Nauman3S/SmartOEESystem/artwork/cdb1.png

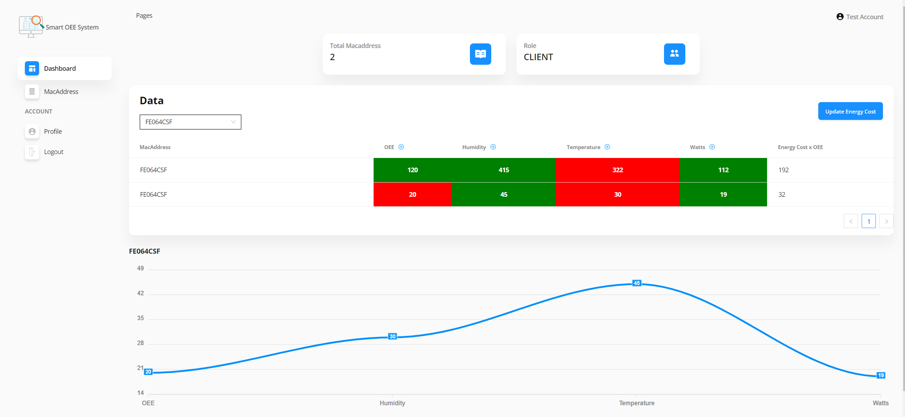
artwork/cdb1.png
