Nauman3S/SmartOEESystem/artwork/cdb2.png

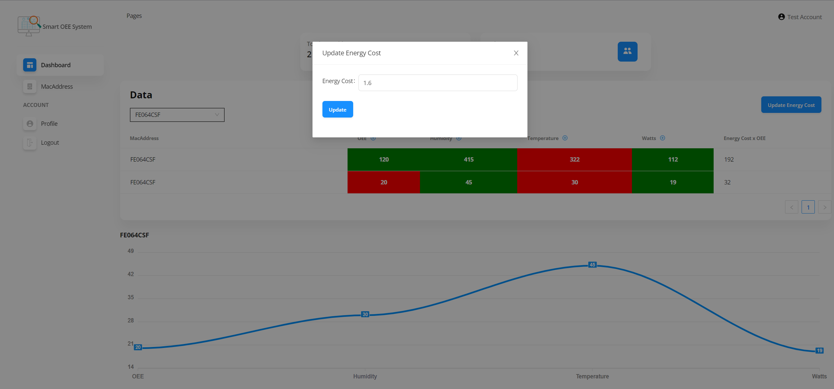
artwork/cdb2.png
