Nauman3S/SmartOEESystem/artwork/cdb3.png

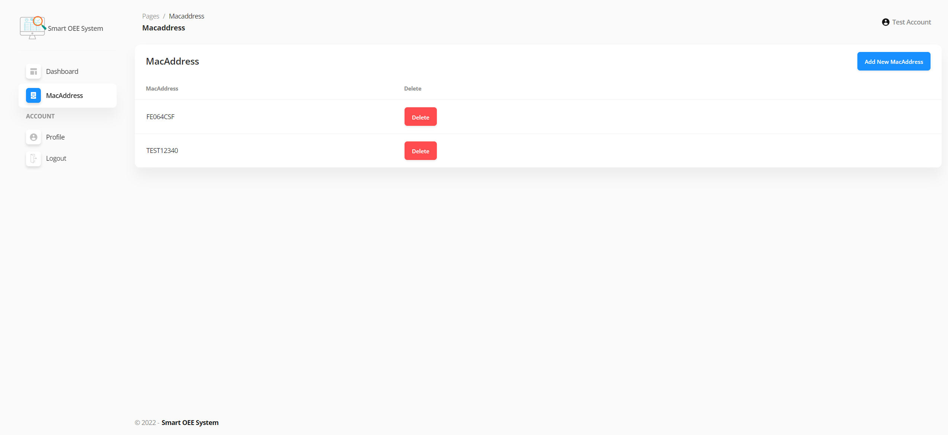
artwork/cdb3.png
