Nauman3S/SmartOEESystem/artwork/cdb4.png

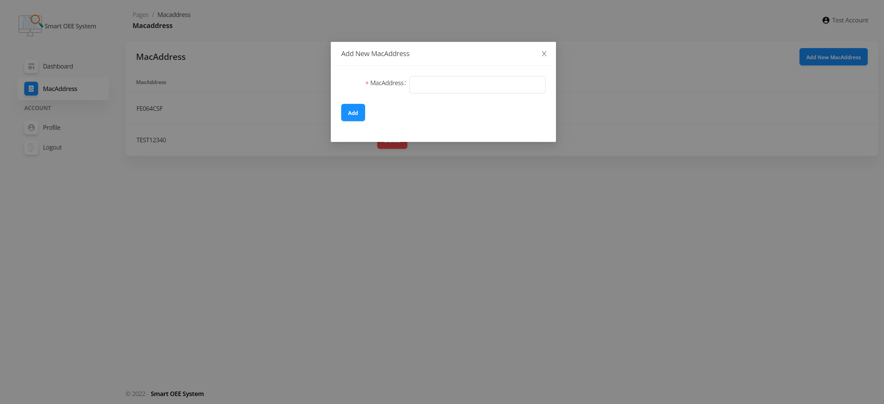
artwork/cdb4.png
