Nauman3S/SmartOEESystem/artwork/db1.png

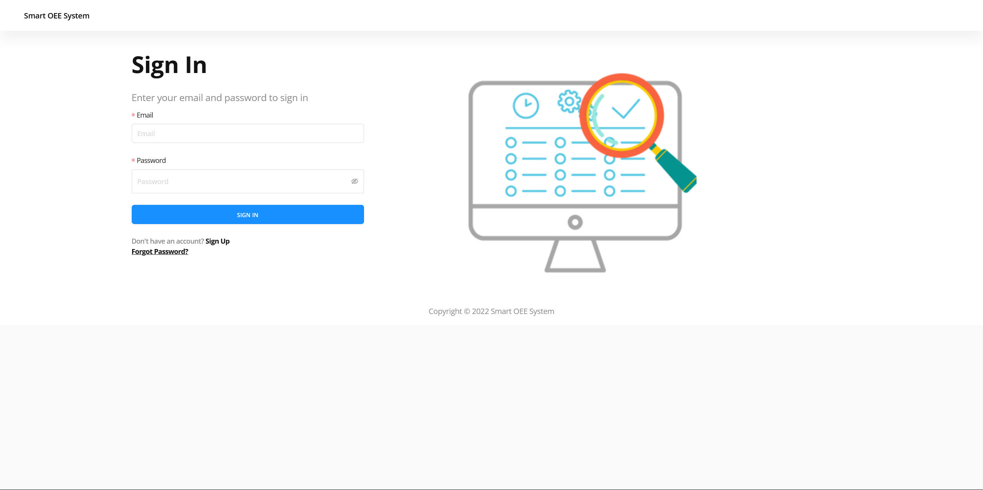
artwork/db1.png
