Nauman3S/SmartOEESystem/artwork/db2.png

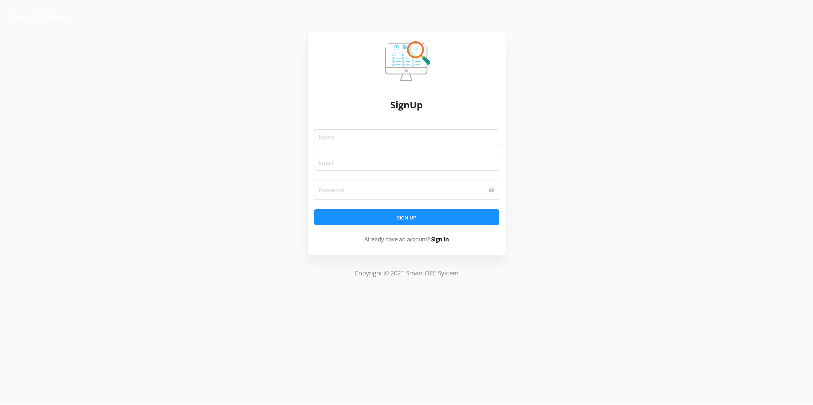
artwork/db2.png
