Nauman3S/SmartOEESystem/artwork/db3.png

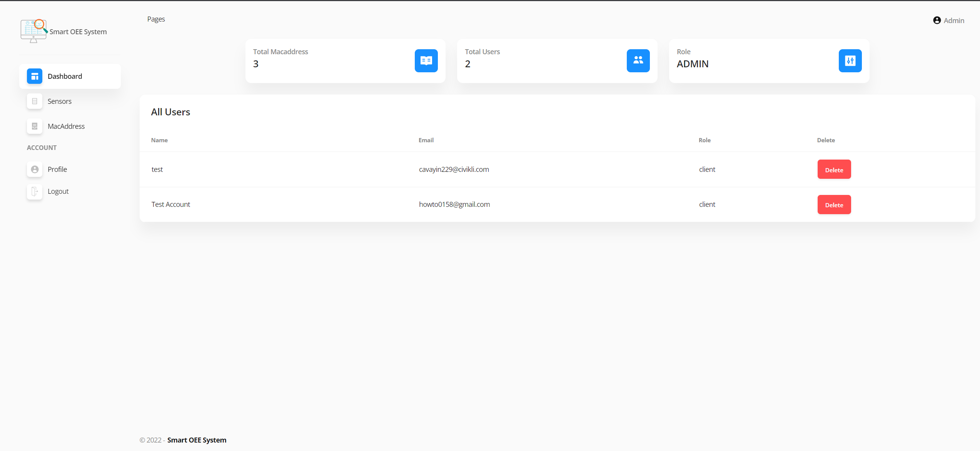
artwork/db3.png
