Nauman3S/SmartOEESystem/artwork/db4.png

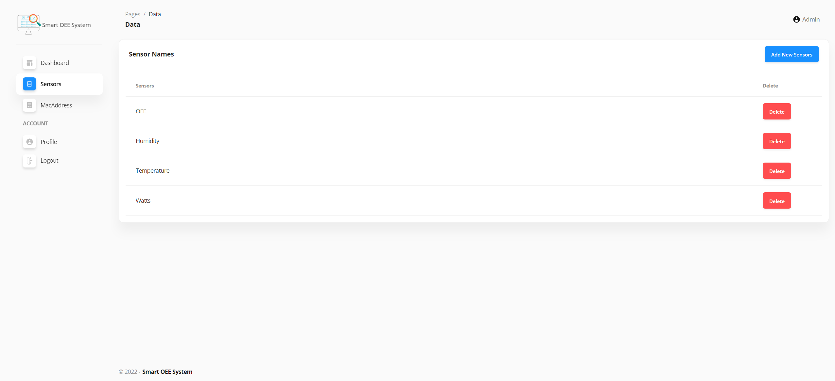
artwork/db4.png
