Nauman3S/SmartOEESystem/artwork/db5.png

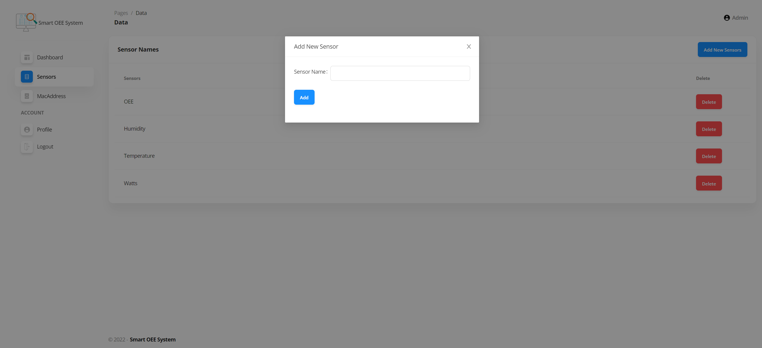
artwork/db5.png
