Nauman3S/SmartOEESystem/artwork/db6.png

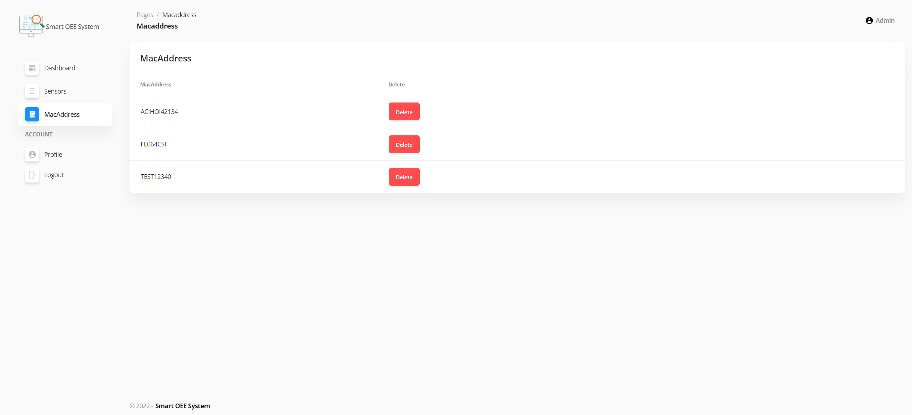
artwork/db6.png
