Nauman3S/SmartOEESystem/artwork/scr2.jpg

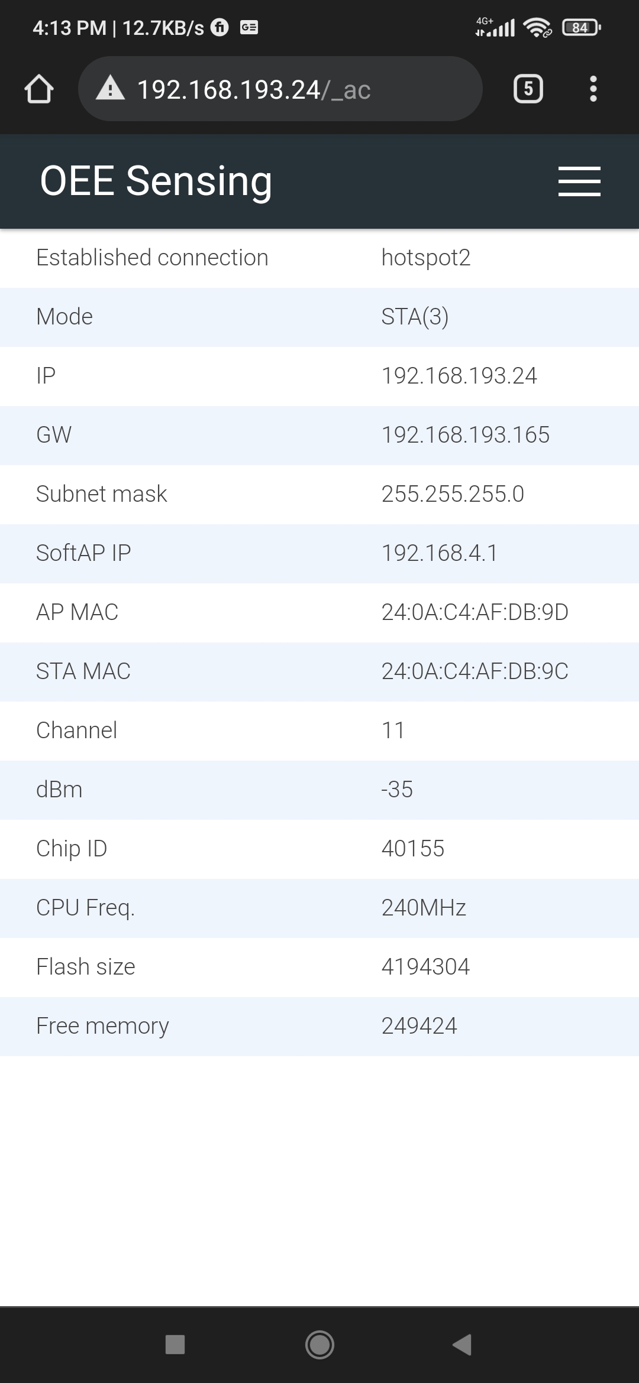
artwork/scr2.jpg
