Nauman3S/SmartOEESystem/artwork/scr3.png

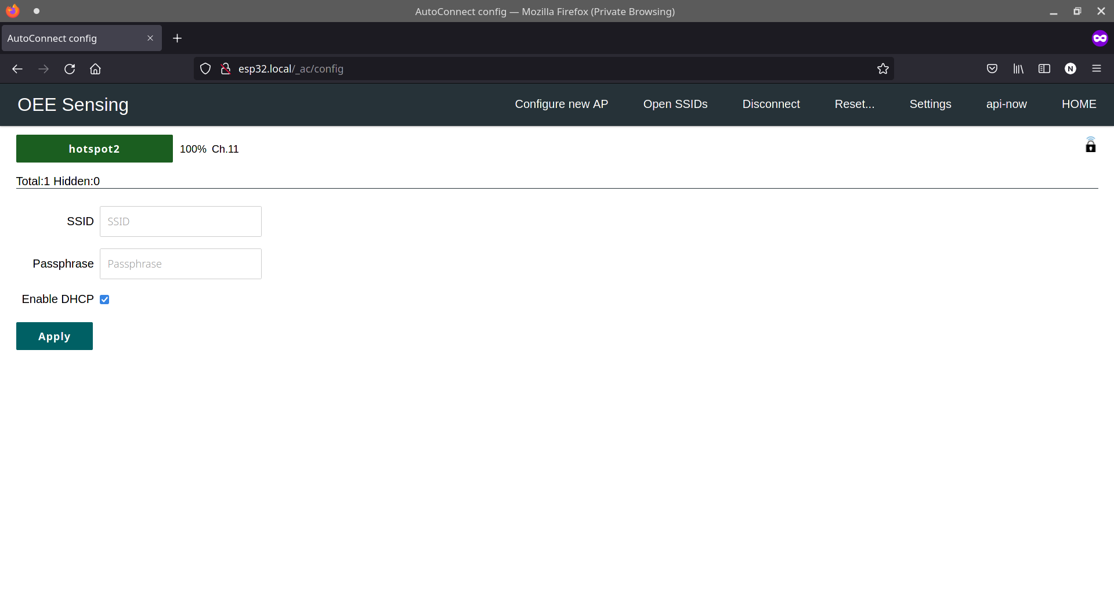
artwork/scr3.png
