Nauman3S/SmartOEESystem/artwork/scr5.png

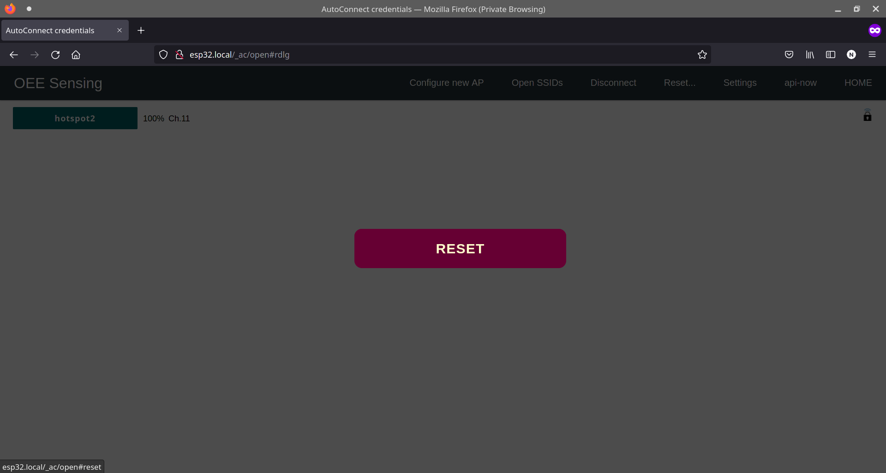
artwork/scr5.png
