Nauman3S/SmartOEESystem/artwork/scr6.png

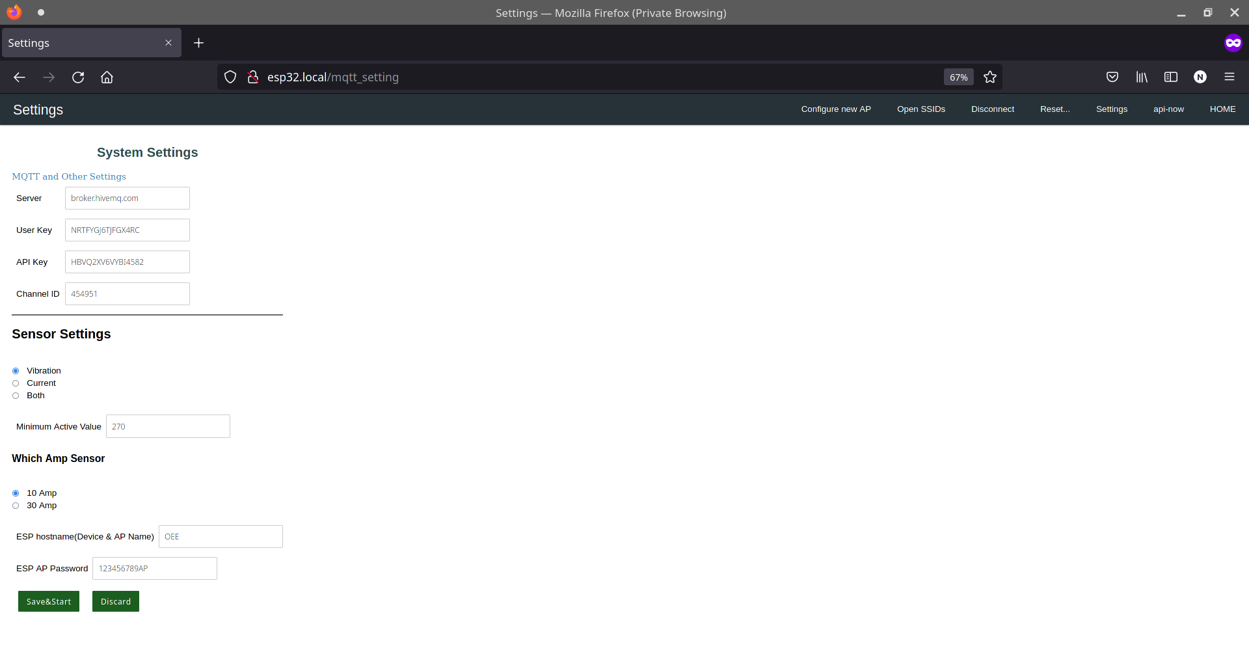
artwork/scr6.png
