Nauman3S/SmartOEESystem/artwork/scr7.png

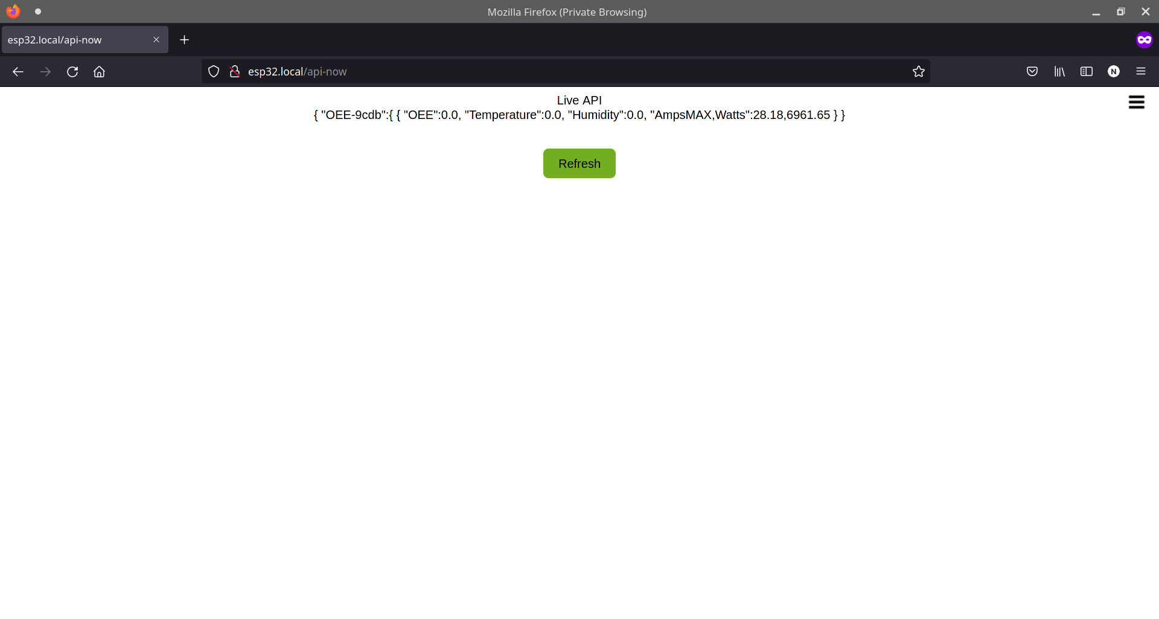
artwork/scr7.png
