Nauman3S/SmartOEESystem/artwork/scr8.png

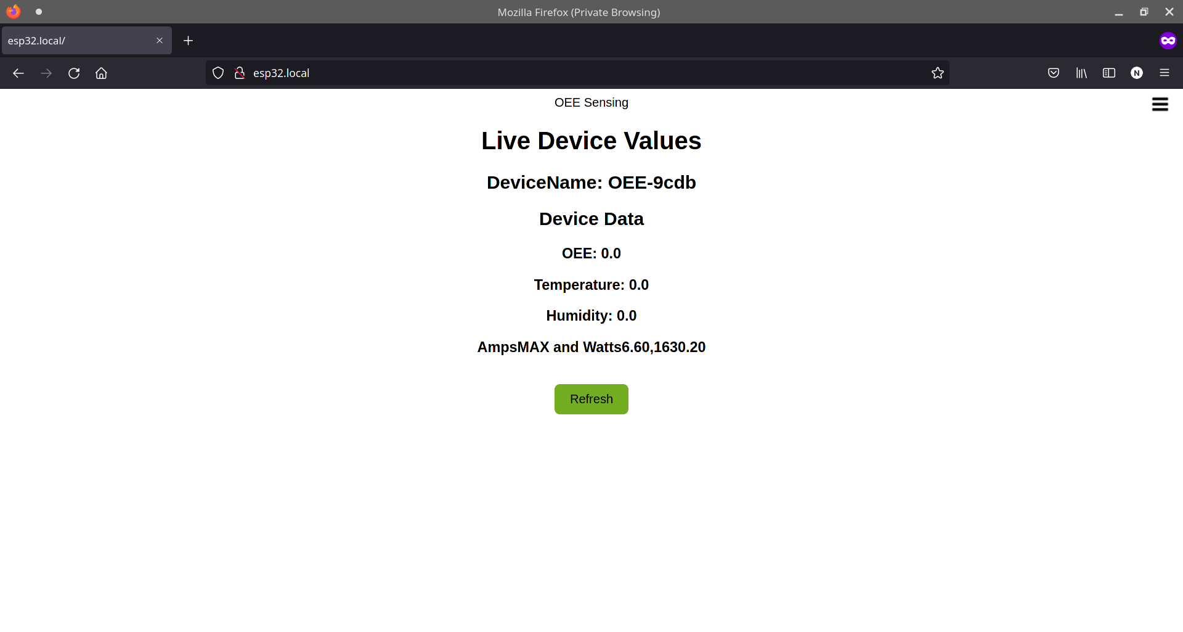
artwork/scr8.png
