Nauman3S/SmartOEESystem/artwork/scr9.png

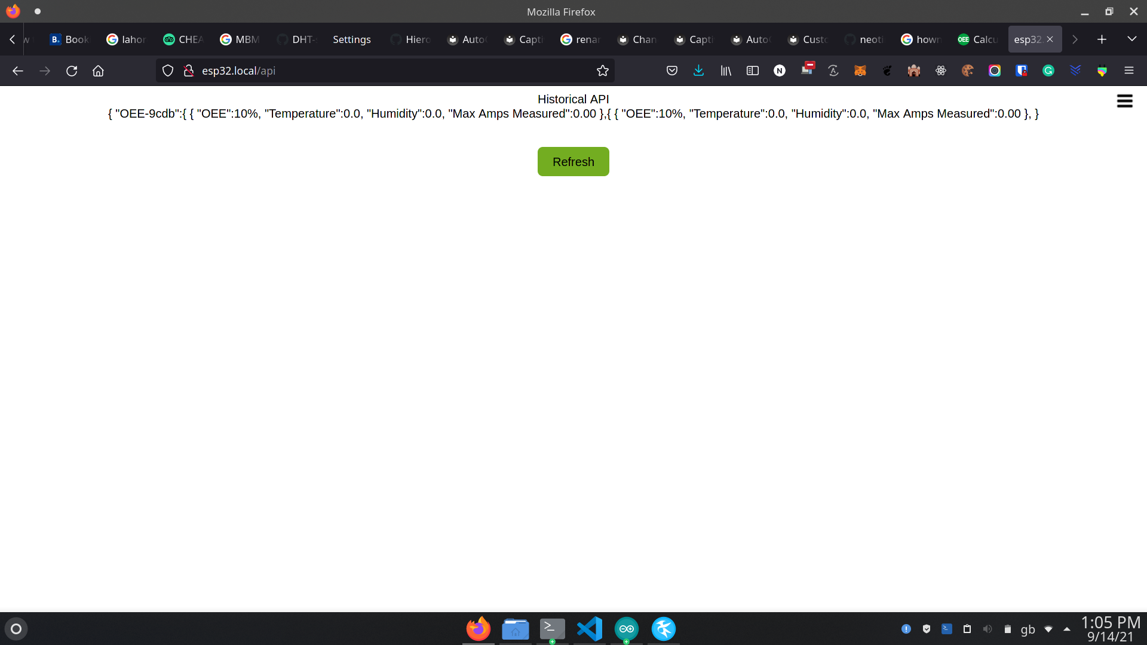
artwork/scr9.png
