Nauman3S/SmartOEESystem/artwork/scr10.png

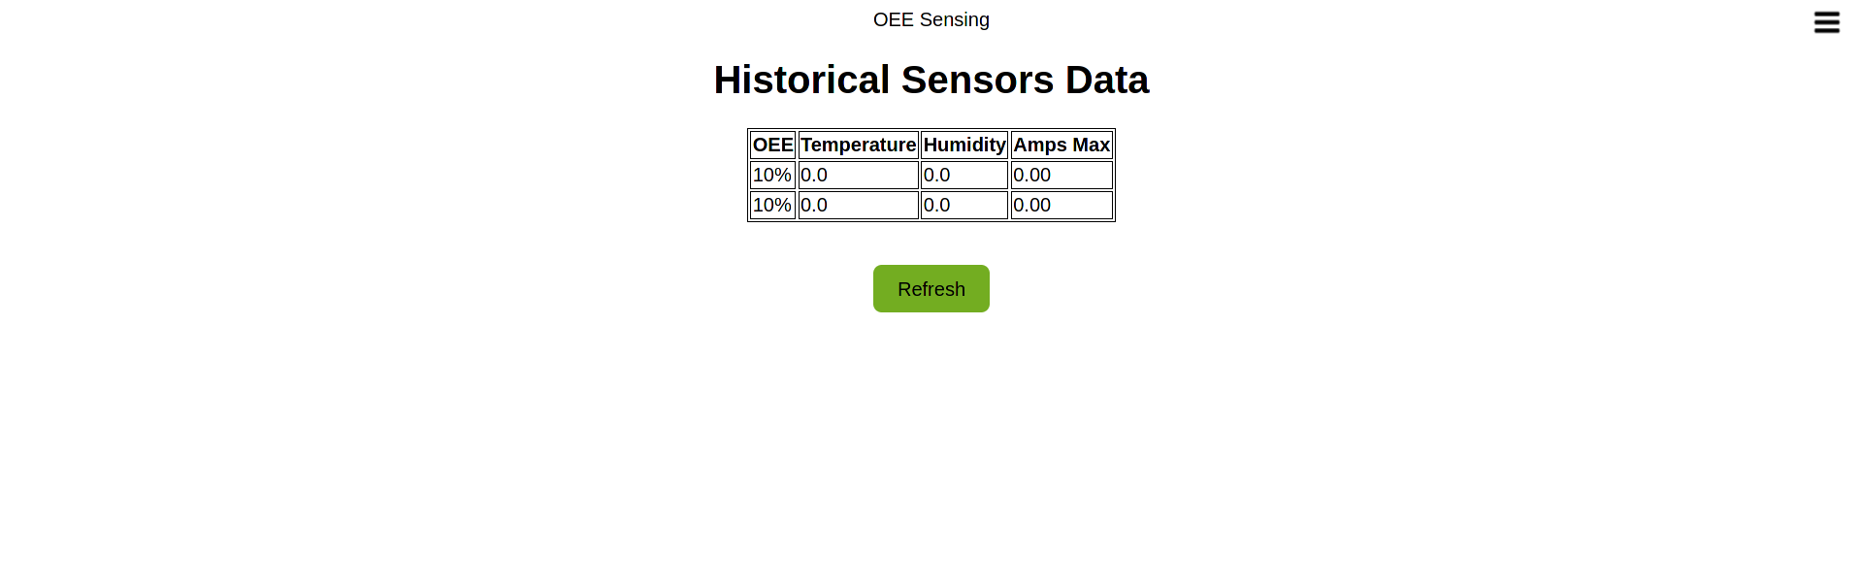
artwork/scr10.png
