Nauman3S/SmartOEESystem/Circuit/ds18b20.jpg

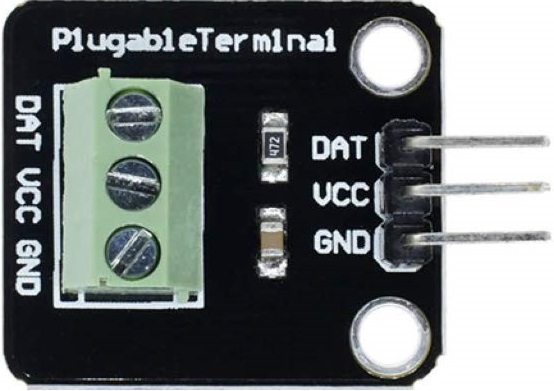
Circuit/ds18b20.jpg
