Nauman3S/SmartOEESystem/Circuit/PCB/pcb_b.png

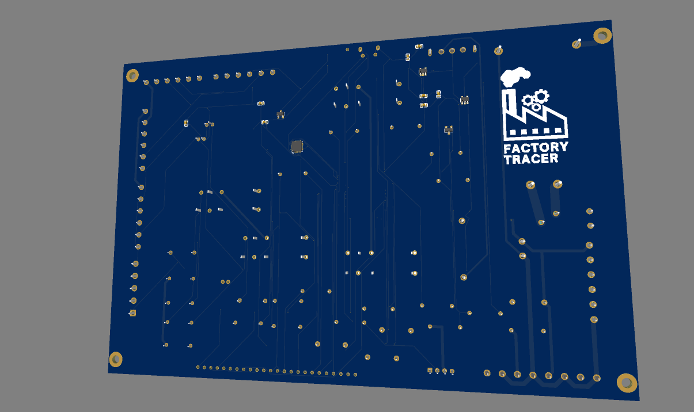
Circuit/PCB/pcb_b.png
