Nauman3S/SmartOEESystem/Circuit/PCB/pcb_f.png

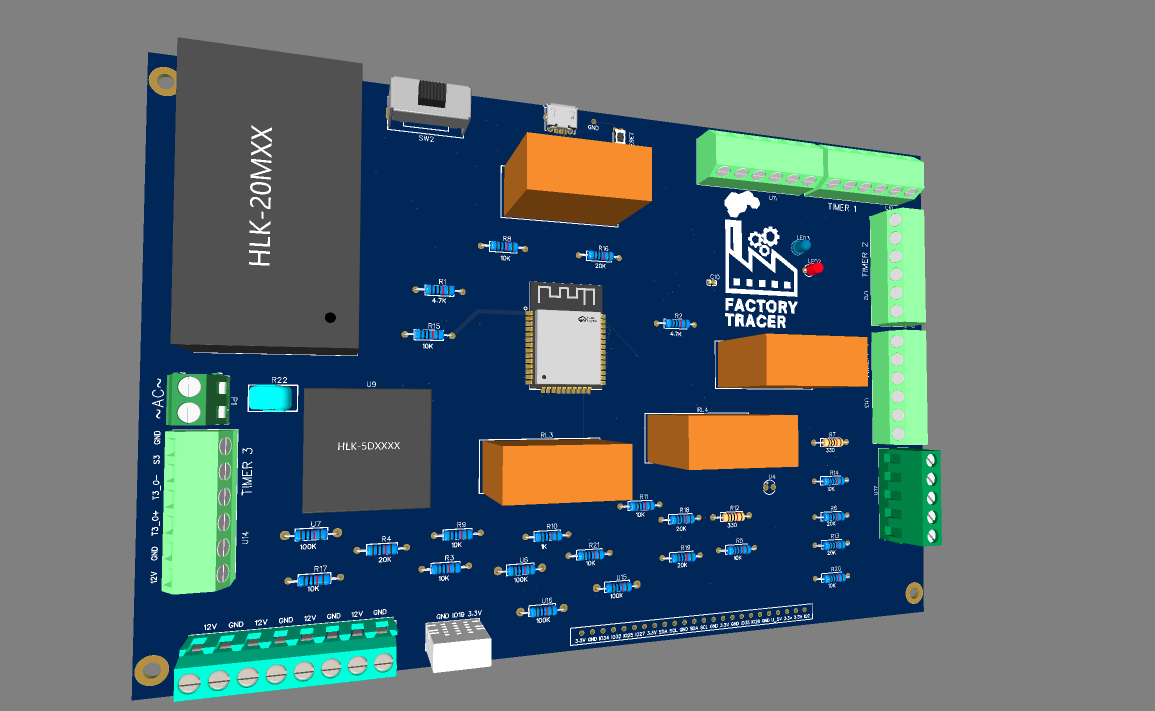
Circuit/PCB/pcb_f.png
