Nauman3S/SmartOEESystem/Circuit/pes.jpg

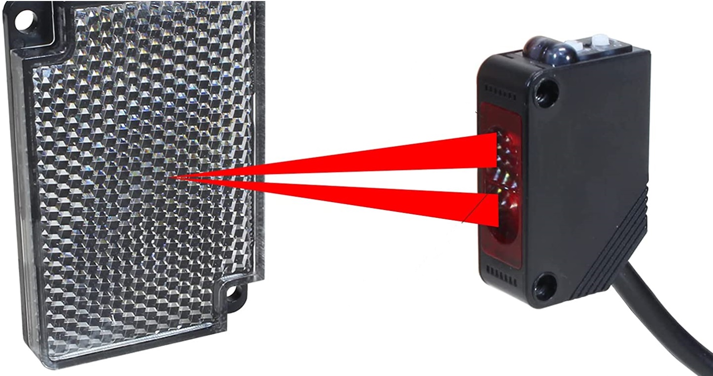
Circuit/pes.jpg
