Nauman3S/SmartOEESystem/temp/Diagram (4).jpg

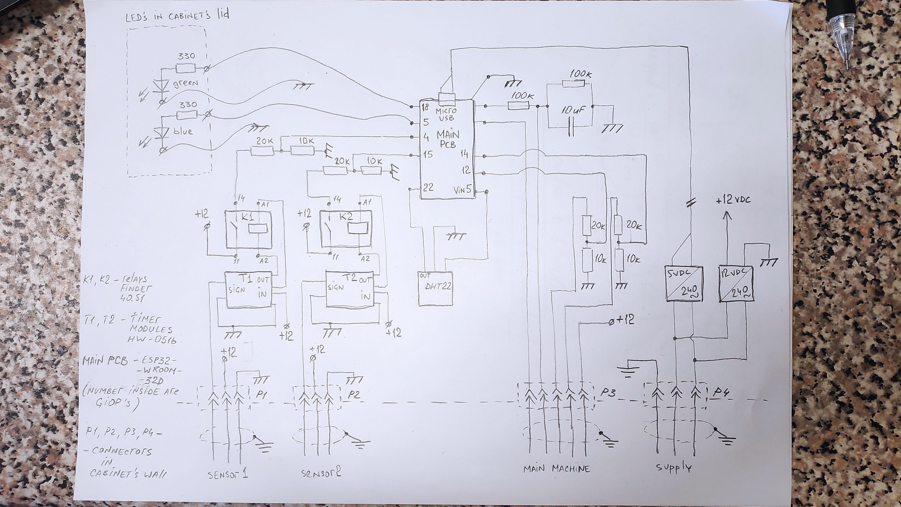
temp/Diagram (4).jpg
