Nauman3S/SmartOEESystem/temp/IOT 2.png

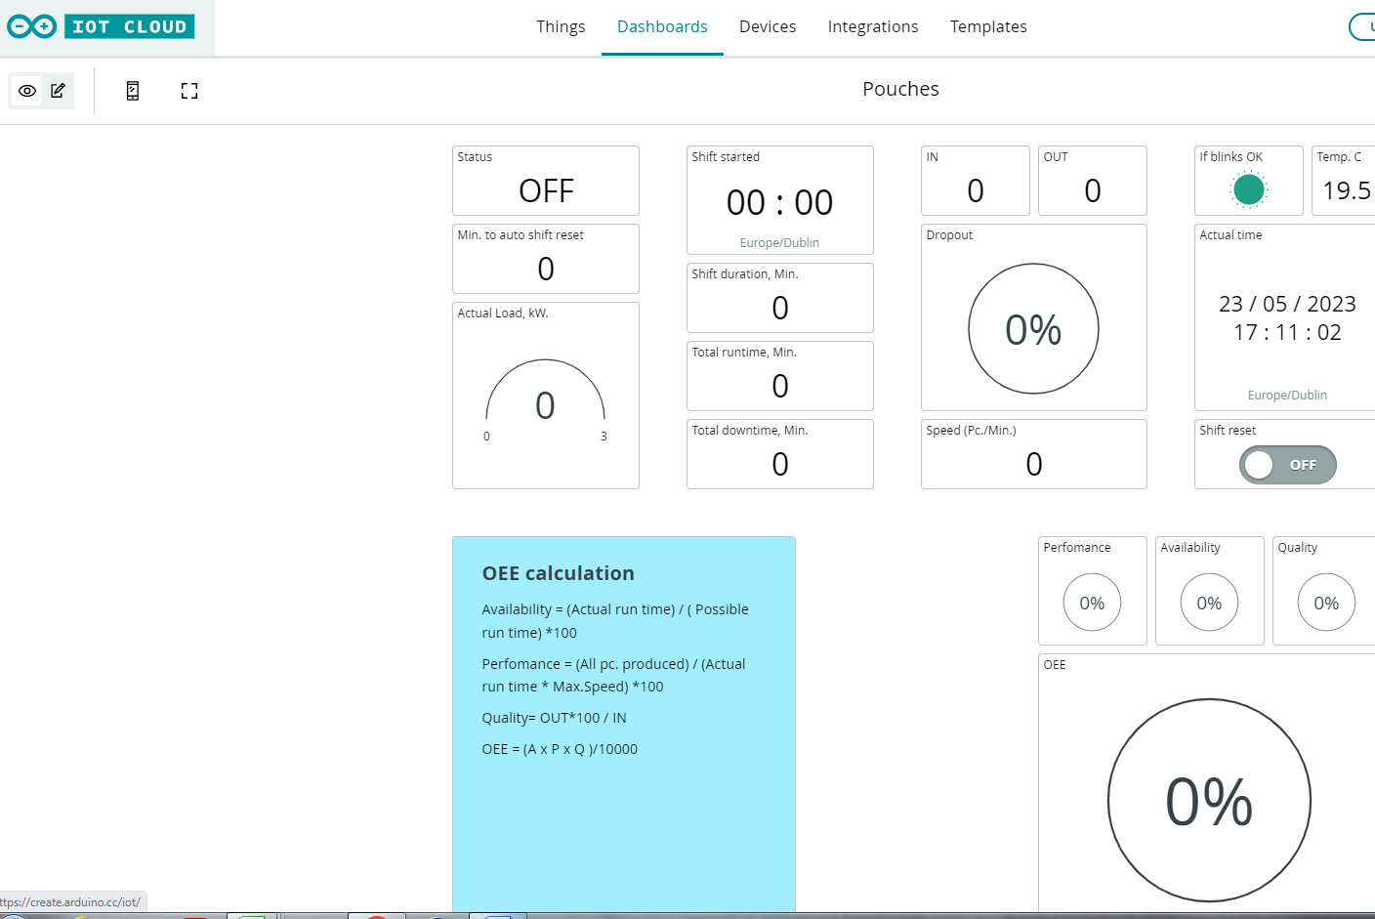
temp/IOT 2.png
