Nauman3S/SmartOEESystem/temp/IOT 3.png

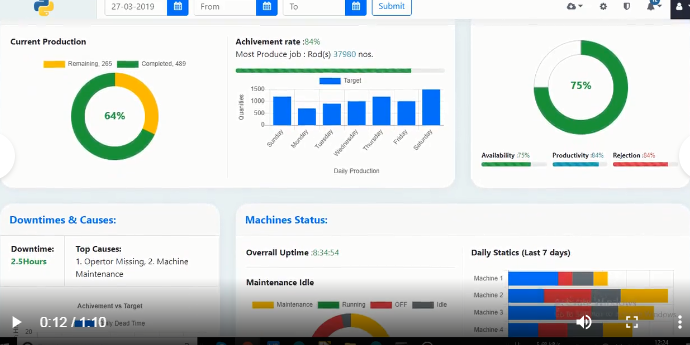
temp/IOT 3.png
