Nauman3S/SmartOEESystem/temp/Line 1.jpg

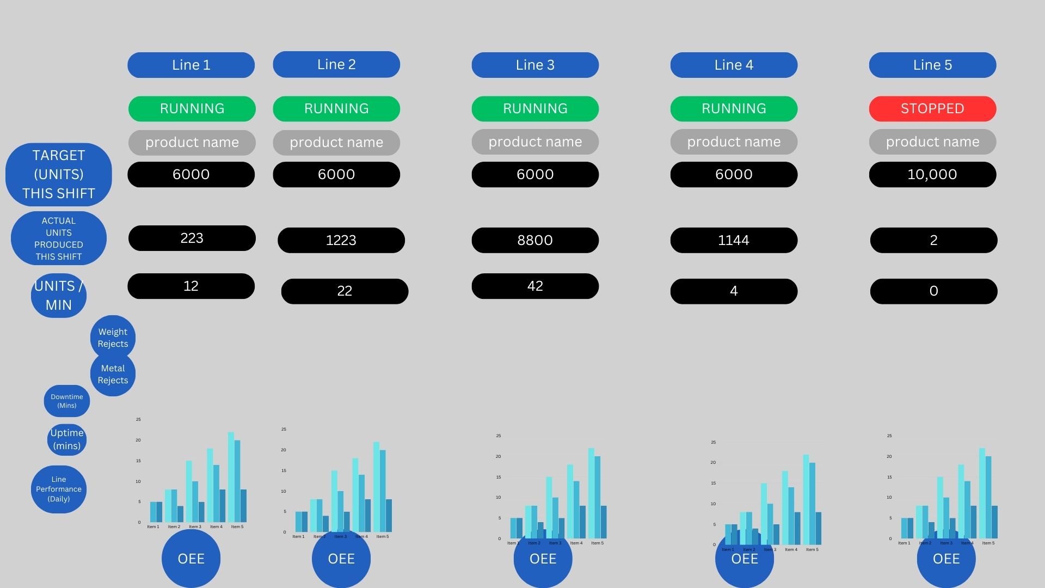
temp/Line 1.jpg
