Nauman3S/SmartOEESystem/temp/paper-dashboard-pro-react-v1.3.2 (1)/paper-dashboard-pro-react-v1.3.2/github-assets/html.png

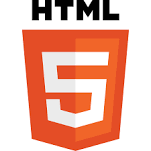
temp/paper-dashboard-pro-react-v1.3.2 (1)/paper-dashboard-pro-react-v1.3.2/github-assets/html.png
