Nauman3S/SmartOEESystem/temp/view (4).jpg

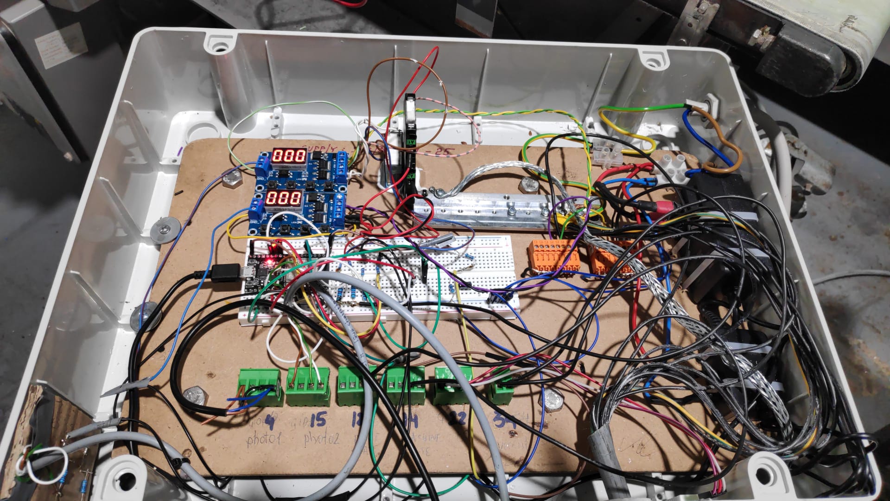
temp/view (4).jpg
