Nauman3S/SmartOEESystem/WebApp/Frontend/src/assets/images/bg-signup.jpg

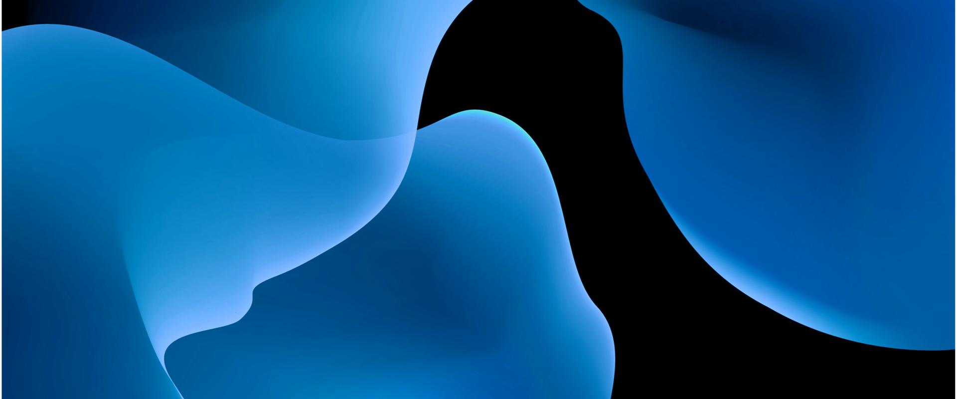
WebApp/Frontend/src/assets/images/bg-signup.jpg
