Nauman3S/SmartOEESystem/WebApp/Frontend/src/assets/images/face-1.jpg

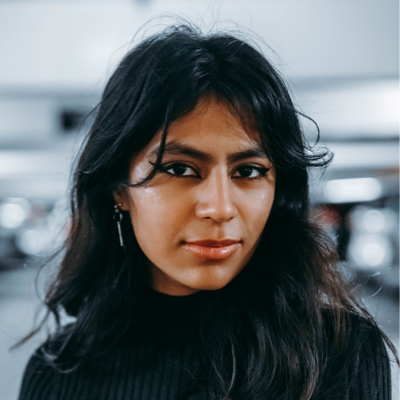
WebApp/Frontend/src/assets/images/face-1.jpg
