Nauman3S/SmartOEESystem/WebApp/Frontend/src/assets/images/face-2.jpg

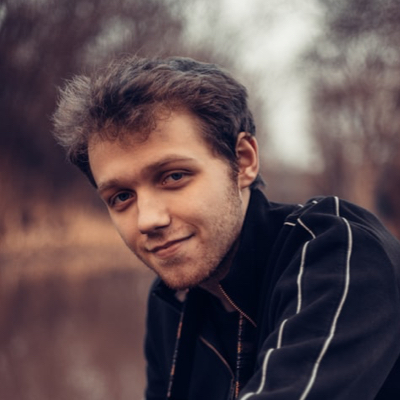
WebApp/Frontend/src/assets/images/face-2.jpg
