Nauman3S/SmartOEESystem/WebApp/Frontend/src/assets/images/face-3.jpg

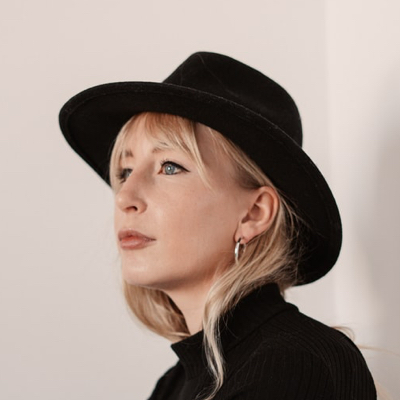
WebApp/Frontend/src/assets/images/face-3.jpg
