Nauman3S/SmartOEESystem/WebApp/Frontend/src/assets/images/face-4.jpg

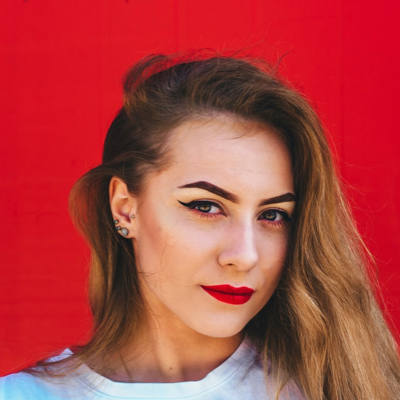
WebApp/Frontend/src/assets/images/face-4.jpg
