Nauman3S/SmartOEESystem/WebApp/Frontend/src/assets/images/face-5.jpeg

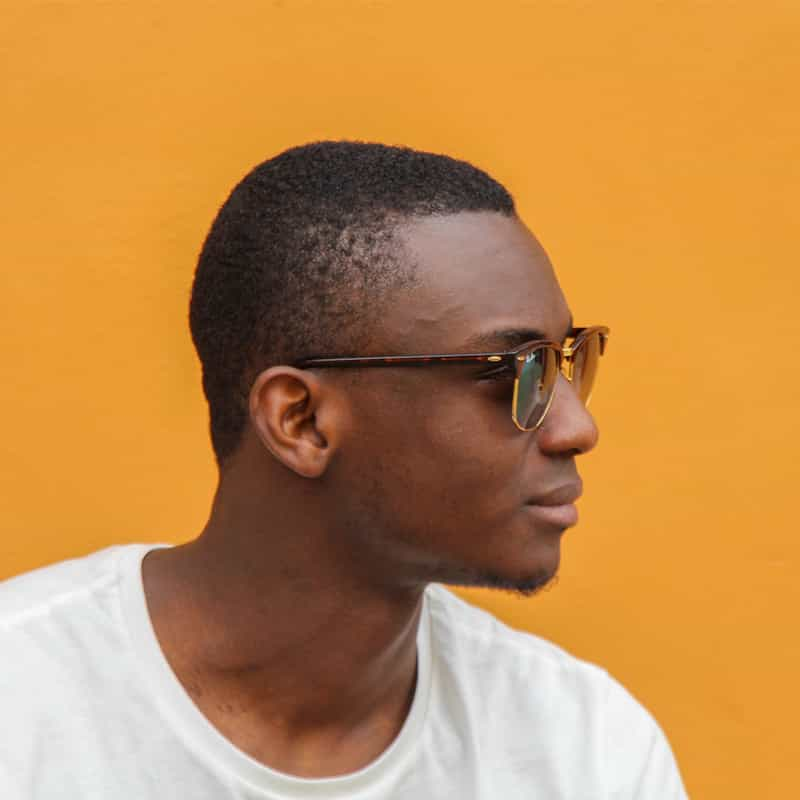
WebApp/Frontend/src/assets/images/face-5.jpeg
