Nauman3S/SmartOEESystem/WebApp/Frontend/src/assets/images/face-6.jpeg

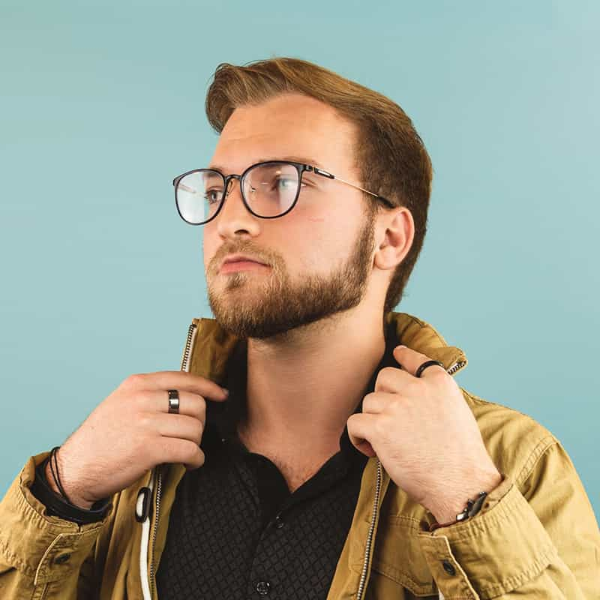
WebApp/Frontend/src/assets/images/face-6.jpeg
