Nauman3S/SmartOEESystem/WebApp/Frontend/src/assets/images/home-decor-1.jpeg

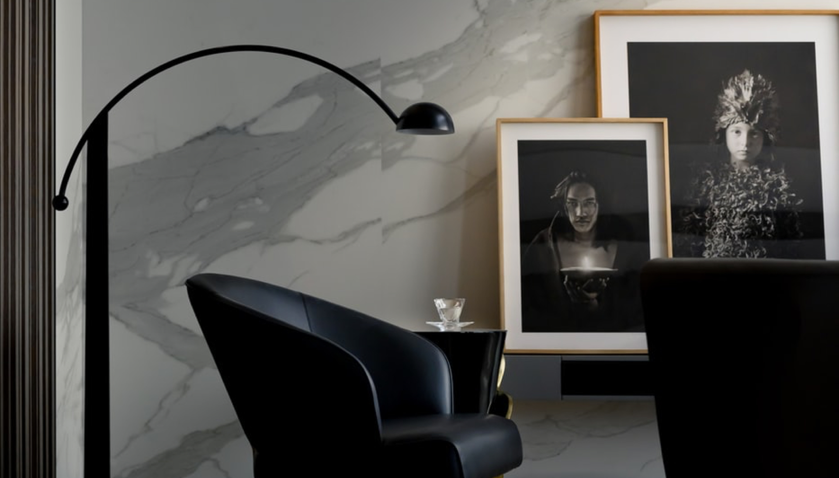
WebApp/Frontend/src/assets/images/home-decor-1.jpeg
