Nauman3S/SmartOEESystem/WebApp/Frontend/src/assets/images/home-decor-2.jpeg

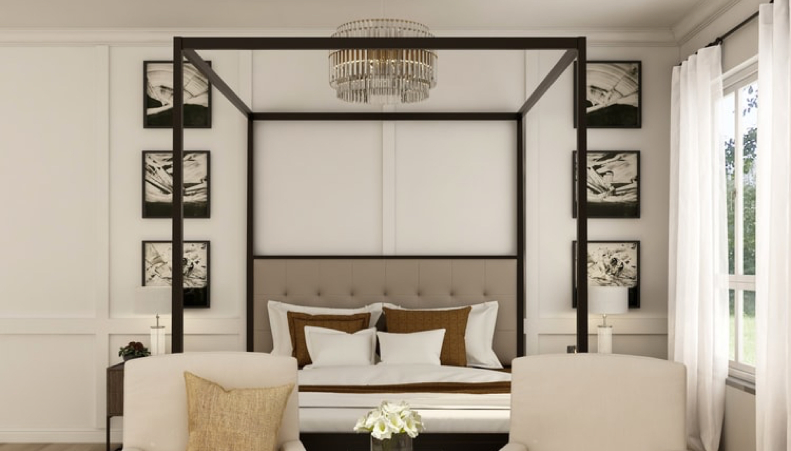
WebApp/Frontend/src/assets/images/home-decor-2.jpeg
