Nauman3S/SmartOEESystem/WebApp/Frontend/src/assets/images/home-decor-3.jpeg

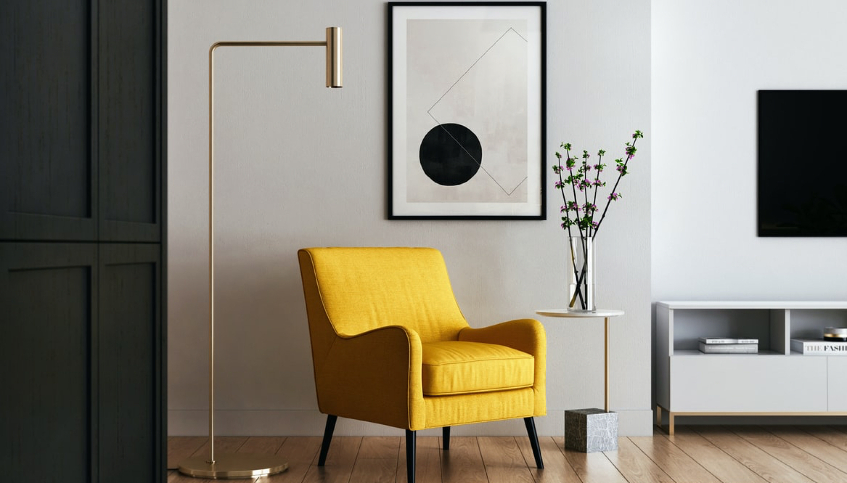
WebApp/Frontend/src/assets/images/home-decor-3.jpeg
