Nauman3S/SmartOEESystem/WebApp/Frontend/src/assets/images/image-statue@2x.png

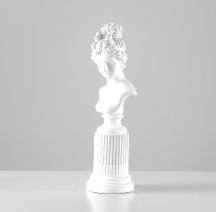
WebApp/Frontend/src/assets/images/image-statue@2x.png
