Nauman3S/SmartOEESystem/WebApp/Frontend/src/assets/images/image@2x.png

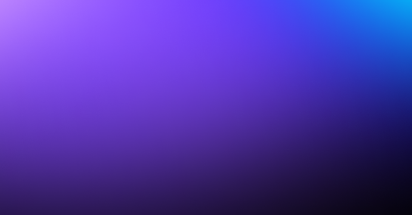
WebApp/Frontend/src/assets/images/image@2x.png
