Nauman3S/SmartOEESystem/WebApp/Frontend/src/assets/images/img-signin.jpg

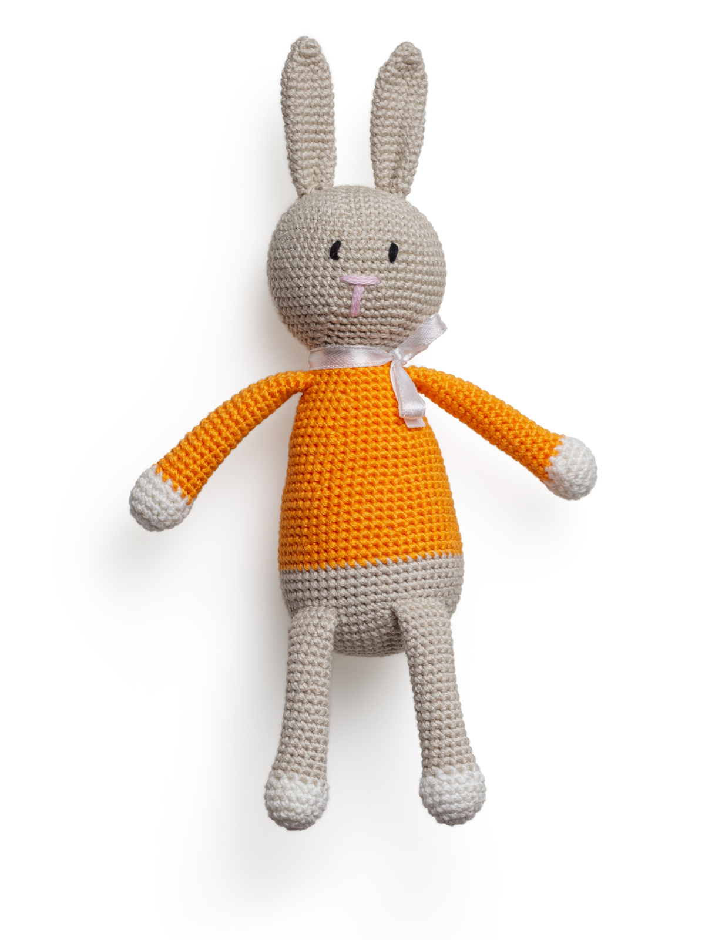
WebApp/Frontend/src/assets/images/img-signin.jpg
