Nauman3S/SmartOEESystem/WebApp/Frontend/src/assets/images/rocket-white.png

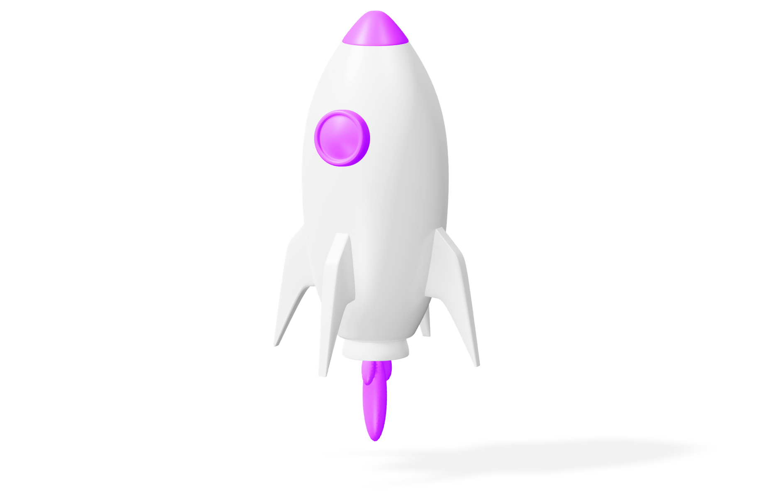
WebApp/Frontend/src/assets/images/rocket-white.png
