Nauman3S/SmartOEESystem/WebApp/Frontend/src/assets/images/team-1.jpg

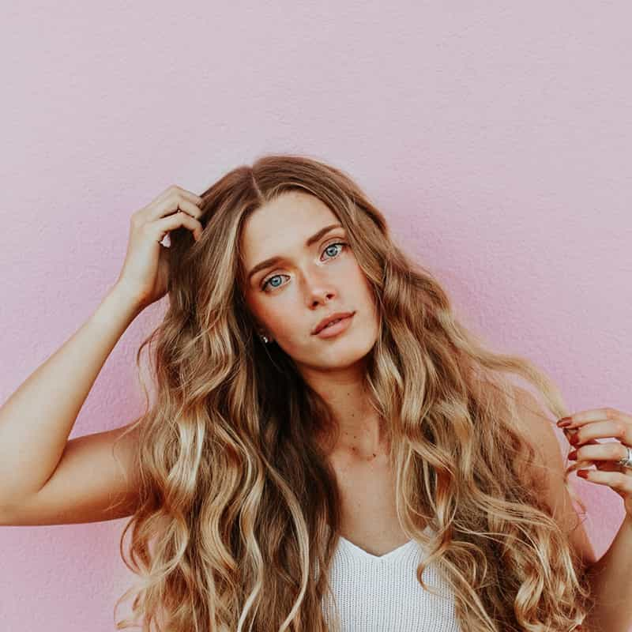
WebApp/Frontend/src/assets/images/team-1.jpg
