Nauman3S/SmartOEESystem/WebApp/Frontend/src/assets/images/team-4.jpg

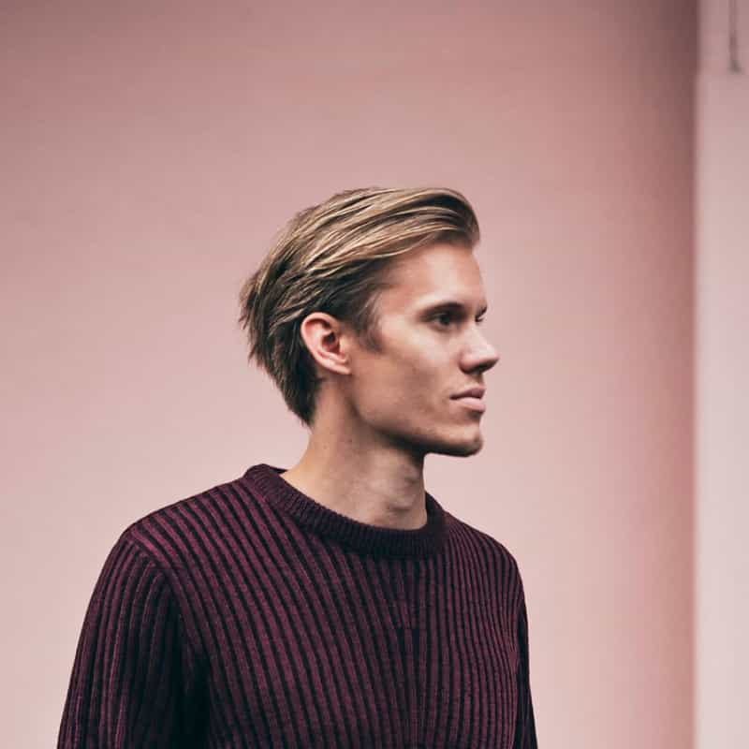
WebApp/Frontend/src/assets/images/team-4.jpg
